barnard704344/3D-Printer-Artillery-Switchwire-Conversion/STL/Electronics/U2c Mount.stl

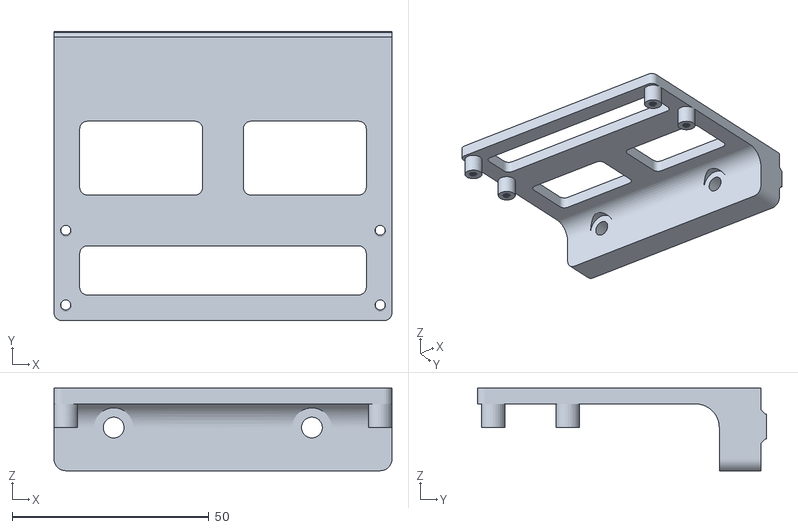
[picture p26: CAD file, 2024-09-25]
STL/Electronics/U2c Mount.stl
86.0 x 73.6 x 21.0
