barnard704344/3D-Printer-Artillery-Switchwire-Conversion/Klipper config/ebb.cfg

# This file contains common pin mappings for the BIGTREETECH EBBCan
# Canbus board. To use this config, the firmware should be compiled for the
# RP2040 with "USB" or "CAN bus (on gpio4/gpio5)".
# The "EBB Can" micro-controller will be used to control the components on the nozzle.

# See docs/Config_Reference.md for a description of parameters.

[mcu EBBCan]
#serial: /dev/serial/by-id/usb-Klipper_Klipper_firmware_12345-if00
#update with your canbus ID
canbus_uuid=6a63161118a2

[temperature_sensor EBB_NTC]
sensor_type: Generic 3950
sensor_pin: EBBCan:gpio28

[adxl345]
cs_pin: EBBCan:gpio1
spi_software_sclk_pin: EBBCan:gpio2
spi_software_mosi_pin: EBBCan:gpio0
spi_software_miso_pin: EBBCan:gpio3
axes_map: z,-y,x

[resonance_tester]
probe_points: 100, 100, 20
accel_chip: adxl345

[extruder]
step_pin: EBBCan:gpio18
dir_pin: EBBCan:gpio19
enable_pin: !EBBCan:gpio17
microsteps: 16
rotation_distance: 4.5
nozzle_diameter: 0.400
filament_diameter: 1.750
heater_pin: EBBCan:gpio7
sensor_type: ATC Semitec 104NT-4-R025H42G
sensor_pin: EBBCan:gpio27
control: pid
pid_Kp: 41.265 
pid_Ki: 5.731 
pid_Kd: 74.277

min_temp: 0
max_temp: 300


[tmc2209 extruder]
uart_pin: EBBCan:gpio20
run_current: 0.5
stealthchop_threshold: 0
#stealthchop_threshold: 999999



[heater_fan hotend_fan]
pin: EBBCan:gpio14
heater: extruder
heater_temp: 50.0
